ViolinLee/PiHexa18/mechanism/Ver.JX-PDI1181MG/ThighBottom.STL

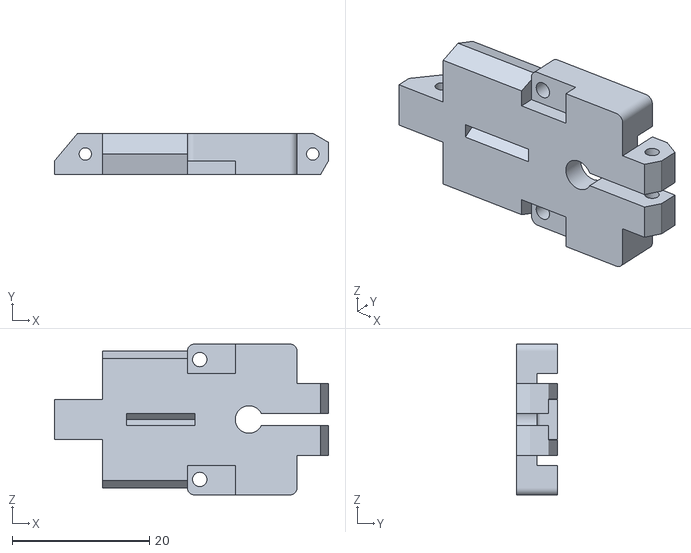
[picture p20: CAD file, 2021-12-25]
mechanism/Ver.JX-PDI1181MG/ThighBottom.STL
40.0 x 6.00 x 22.0
