ViolinLee/PiHexa18/mechanism/Ver.GuoHua-A0090/LegTop.STL

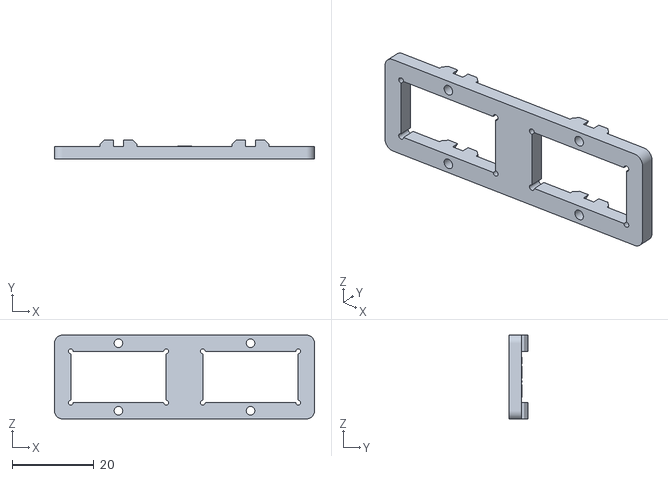
[picture p21: CAD file, 2021-11-15]
mechanism/Ver.GuoHua-A0090/LegTop.STL
63.8 x 4.60 x 20.6
