ViolinLee/PiHexa18/mechanism/Ver.JX-PDI1181MG/JointDown.STL

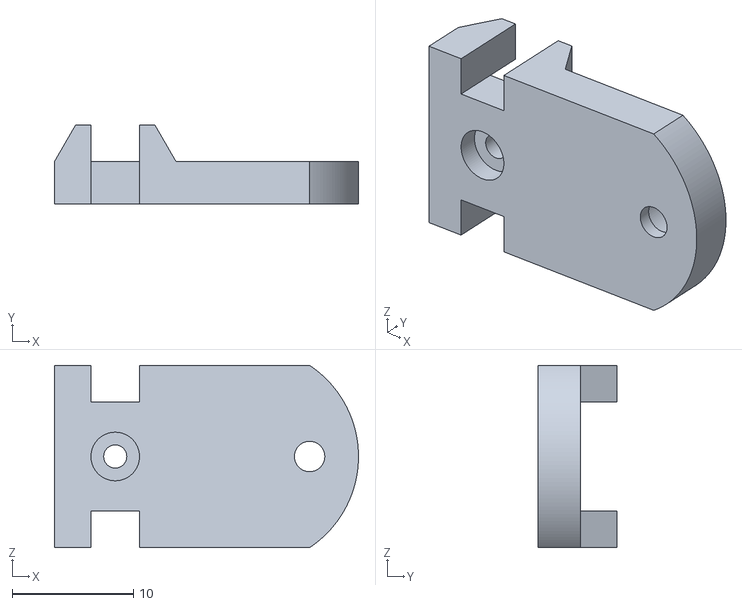
[picture p22: CAD file, 2021-12-25]
mechanism/Ver.JX-PDI1181MG/JointDown.STL
25.0 x 6.50 x 15.0
