ViolinLee/PiHexa18/mechanism/Ver.GuoHua-A0090/LegBottom.STL

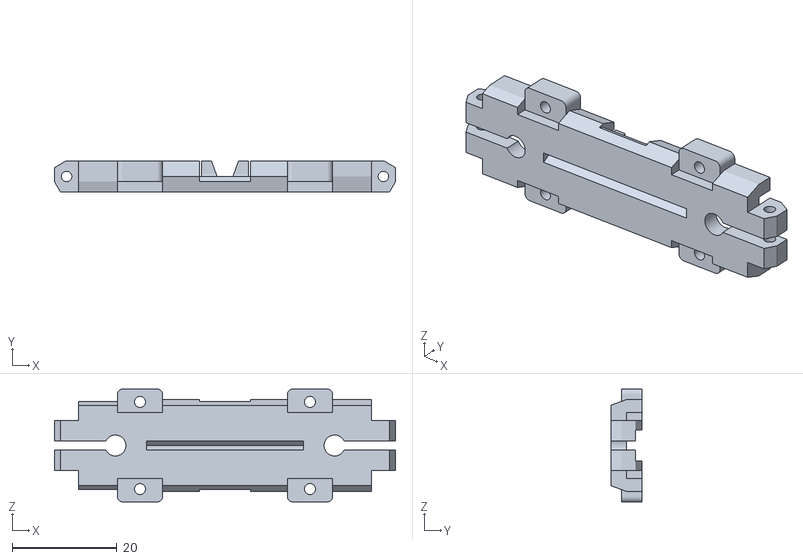
[picture p23: CAD file, 2021-11-15]
mechanism/Ver.GuoHua-A0090/LegBottom.STL
65.0 x 6.00 x 21.5
