ViolinLee/PiHexa18/mechanism/Ver.JX-PDI1181MG/LegBottom.STL

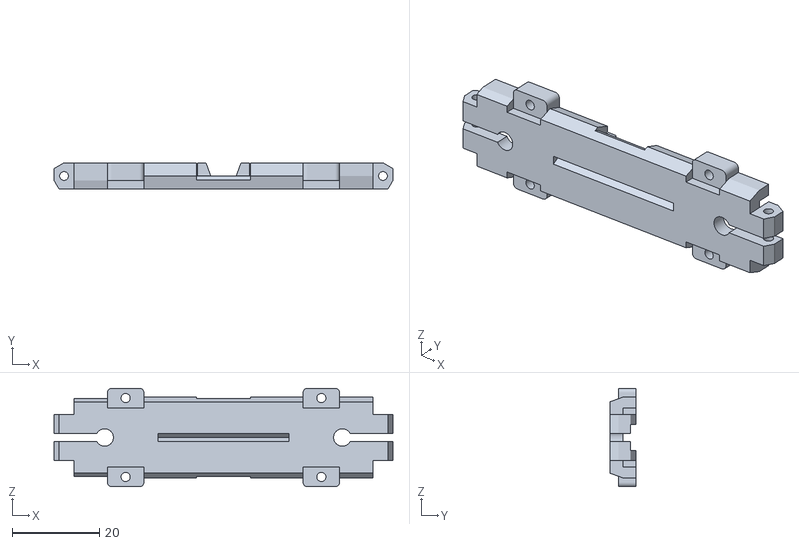
[picture p24: CAD file, 2021-12-25]
mechanism/Ver.JX-PDI1181MG/LegBottom.STL
77.6 x 6.00 x 22.5
