ViolinLee/PiHexa18/mechanism/Ver.GuoHua-A0090/ThighBottom.STL

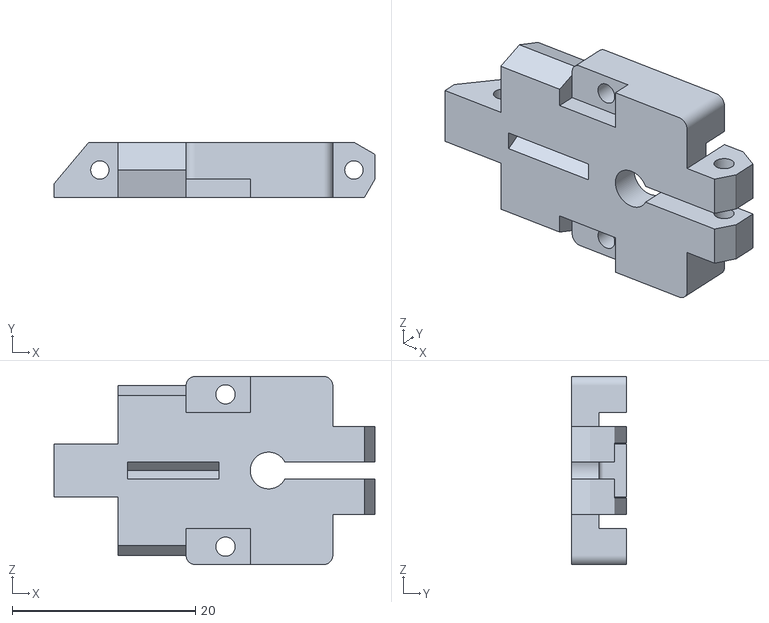
[picture p25: CAD file, 2021-11-15]
mechanism/Ver.GuoHua-A0090/ThighBottom.STL
35.0 x 6.00 x 20.5
