ViolinLee/PiHexa18/mechanism/Ver.JX-PDI1181MG/JointTop.STL

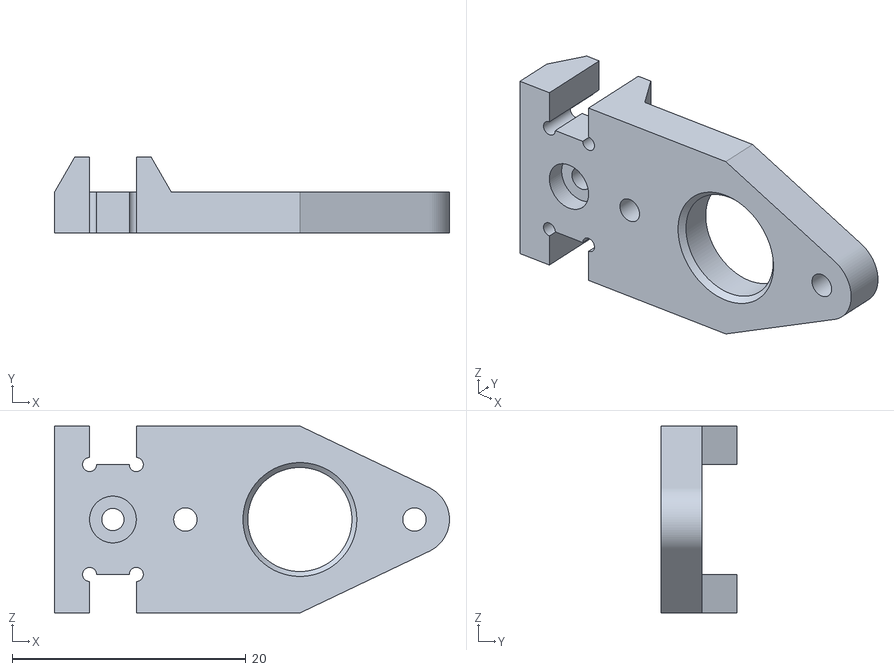
[picture p26: CAD file, 2021-12-25]
mechanism/Ver.JX-PDI1181MG/JointTop.STL
33.8 x 6.50 x 16.0
