ViolinLee/PiHexa18/mechanism/Ver.JX-PDI1181MG/BodySideWall.STL

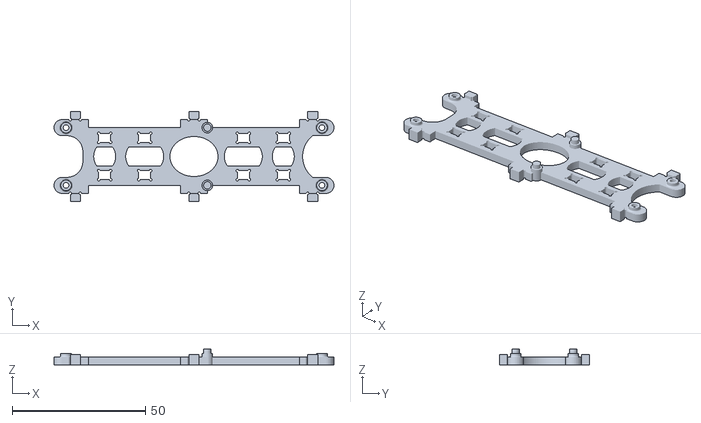
[picture p27: CAD file, 2021-12-23]
mechanism/Ver.JX-PDI1181MG/BodySideWall.STL
105.0 x 33.7 x 6.00
