ViolinLee/PiHexa18/mechanism/Ver.JX-PDI1181MG/BodyCenter.STL

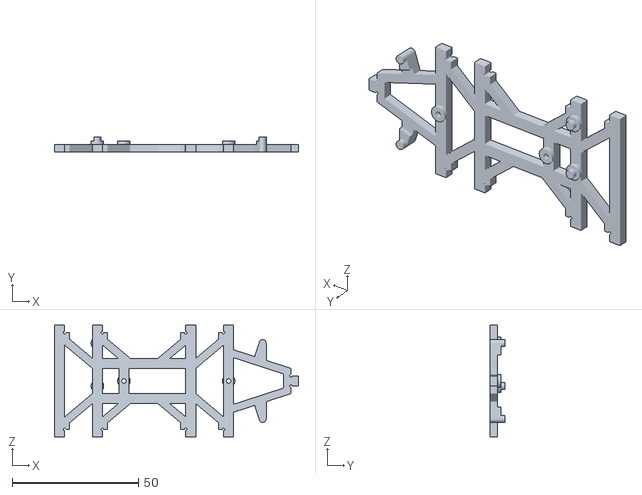
[picture p28: CAD file, 2021-12-23]
mechanism/Ver.JX-PDI1181MG/BodyCenter.STL
96.7 x 6.00 x 44.3
