ViolinLee/PiHexa18/mechanism/Ver.JX-PDI1181MG/FootTip.STL

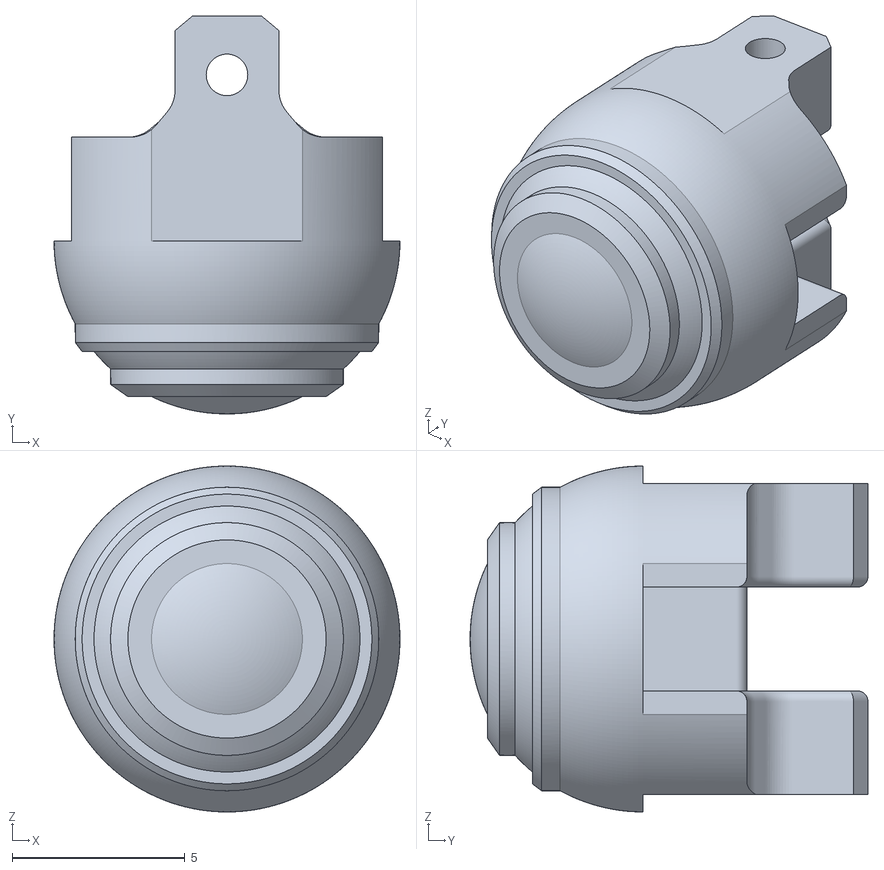
[picture p29: CAD file, 2021-12-23]
mechanism/Ver.JX-PDI1181MG/FootTip.STL
10.0 x 11.5 x 10.00
