ViolinLee/PiHexa18/mechanism/Ver.JX-PDI1181MG/BodyBackWall.STL

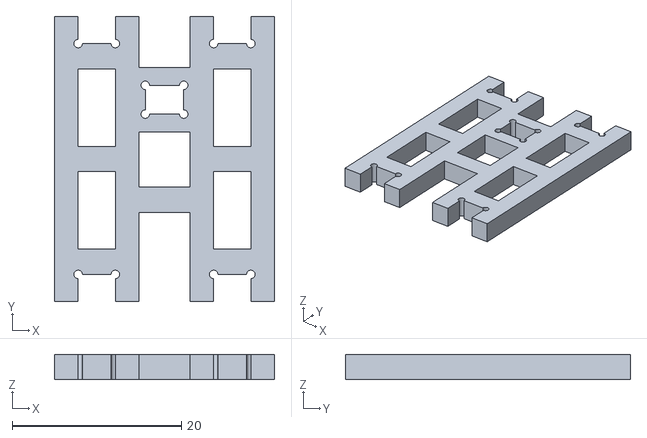
[picture p30: CAD file, 2021-12-22]
mechanism/Ver.JX-PDI1181MG/BodyBackWall.STL
26.0 x 33.7 x 3.00
