ViolinLee/PiHexa18/mechanism/Ver.JX-PDI1181MG/BodyButtom.STL

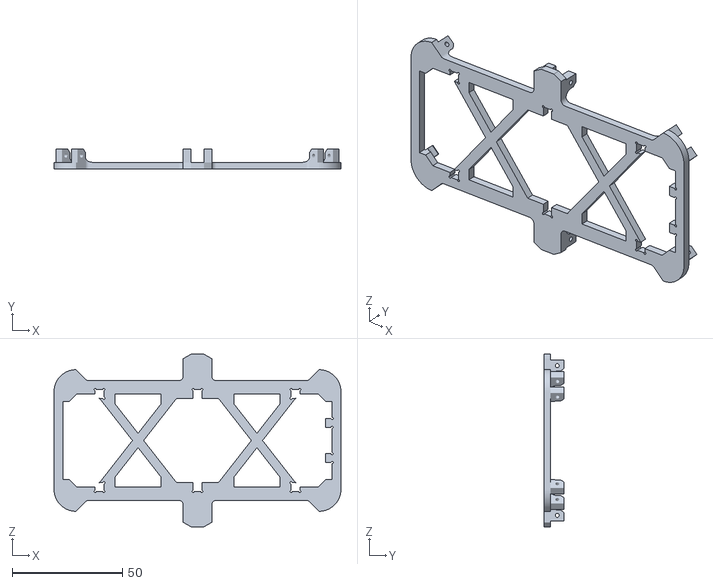
[picture p31: CAD file, 2021-12-22]
mechanism/Ver.JX-PDI1181MG/BodyButtom.STL
130.3 x 9.00 x 78.3
