ViolinLee/PiHexa18/pihexa/leg.py

# -*- coding: utf-8 -*-

from config import *
from math_utils import *
from math import sin, cos, pi, atan2, sqrt, acos


hpi = pi/2


class BaseLeg(object):
    def __init__(self, leg_index):
        self._leg_index = leg_index
        """ 
        local_conv: 世界坐标系上的表达转换到本地坐标系上的表达
        world_conv: 本地坐标系上的表达转换到世界坐标系上的表达
        """
        if self._leg_index == 0:  # 45 or -315 degree:
            self._mount_position = point3d(leg_mount_other_x, leg_mount_other_y, 0)
            self._local_conv = rotate315  # local_P = R(local上world下，world在local上的描述) * world_P
            self._world_conv = rotate45  # world_P = R(world上local下，local在world上的描述) * local_P
            self._tip_pos_local = point3d(p1_x, p1_y, p1_z)
            self._tip_pos = self.translate2world(self._tip_pos_local)
        elif self._leg_index == 1:  # 0 degree:
            self._mount_position = point3d(leg_mount_left_right_x, 0, 0)
            self._local_conv = rotate0
            self._world_conv = rotate0
            self._tip_pos_local = point3d(p2_x, p2_y, p2_z)
            self._tip_pos = self.translate2world(self._tip_pos_local)
        elif self._leg_index == 2:  # -45 or 315 degree:
            self._mount_position = point3d(leg_mount_other_x, -leg_mount_other_y, 0)
            self._local_conv = rotate45
            self._world_conv = rotate315
            self._tip_pos_local = point3d(p3_x, p3_y, p3_z)
            self._tip_pos = self.translate2world(self._tip_pos_local)
        elif self._leg_index == 3:  # -135 or 225 degree:
            self._mount_position = point3d(-leg_mount_other_x, -leg_mount_other_y, 0)
            self._local_conv = rotate135
            self._world_conv = rotate225
            self._tip_pos_local = point3d(p4_x, p4_y, p4_z)
            self._tip_pos = self.translate2world(self._tip_pos_local)
        elif self._leg_index == 4:  # -180 or 180 degree:
            self._mount_position = point3d(-leg_mount_left_right_x, 0, 0)
            self._local_conv = rotate180
            self._world_conv = rotate180
            self._tip_pos_local = point3d(p5_x, p5_y, p5_z)
            self._tip_pos = self.translate2world(self._tip_pos_local)
        elif self._leg_index == 5:  # -225 or 135 degree:
            self._mount_position = point3d(-leg_mount_other_x, leg_mount_other_y, 0)
            self._local_conv = rotate225
            self._world_conv = rotate135
            self._tip_pos_local = point3d(p6_x, p6_y, p6_z)
            self._tip_pos = self.translate2world(self._tip_pos_local)
        else:
            raise ValueError

    """coordinate system translation"""
    def translate2local(self, world_point: point3d):
        return self._local_conv(world_point - self._mount_position)

    def translate2world(self, local_point: point3d):
        return self._world_conv(local_point) + self._mount_position

    @staticmethod
    def inverse_kinematics(target_point: point3d):
        """坐标原点在根部舵机安装处"""
        angles = [0.0] * 3

        x = target_point.x - leg_root2joint1
        y = target_point.y
        angles[0] = atan2(y, x) * 180 / pi

        x = sqrt(x**2 + y**2) - leg_joint1_2joint2
        y = target_point.z
        ar = atan2(y, x)
        lr2 = x**2 + y**2
        lr = sqrt(lr2)
        a1 = acos((lr2 + leg_joint2_2joint3**2 - leg_joint3_2tip**2) / (2 * leg_joint2_2joint3 * lr))
        a2 = acos((lr2 - leg_joint2_2joint3**2 + leg_joint3_2tip**2) / (2 * leg_joint3_2tip * lr))
        angles[1] = (ar + a1) * 180 / pi
        angles[2] = 90 - ((a1 + a2) * 180 / pi)

        return angles

    def get_tip_position_local(self):
        return self._tip_pos_local


class RealLeg(BaseLeg):
    """
    定义六足机器人单腿类，包括基坐标转换和正逆运动学相关类函数。
    """
    def __init__(self, leg_index, leg_servo):
        super().__init__(leg_index)
        self._leg_servo = leg_servo

    """forward and inverse kinematics calculations are below local coordinate"""
    @staticmethod
    def forward_kinematics(angles):
        radians = [angle * pi / 180 for angle in angles]
        x = leg_joint1_2joint2 + cos(radians[1]) * leg_joint2_2joint3 + cos(radians[1] + radians[2] - hpi) * leg_joint3_2tip

        out_point = point3d()
        out_point.x = leg_root2joint1 + cos(radians[0]) * x
        out_point.y = sin(radians[0]) * x
        out_point.z = sin(radians[1]) * leg_joint2_2joint3 + sin(radians[1] + radians[2] - hpi) * leg_joint3_2tip

        return out_point

    def set_joint_angle(self, angles):
        out_point = self.forward_kinematics(angles)
        self.move_tip_local(out_point)

    def move_tip(self, target_point_world: point3d):
        """word coordiante system (default)"""
        if target_point_world == self._tip_pos:
            return
        dest_local = self.translate2local(target_point_world)
        # logging info
        self.__move(dest_local)
        self._tip_pos = target_point_world
        self._tip_pos_local = dest_local

    def get_tip_position(self):
        return self._tip_pos

    def move_tip_local(self, target_point_local: point3d):
        """local coordinate system version"""
        if target_point_local == self._tip_pos_local:
            return
        dest_world = self.translate2world(target_point_local)
        self.__move(target_point_local)
        self._tip_pos = dest_world
        self._tip_pos_local = target_point_local

    def __move(self, target_point_local: point3d):
        angles = self.inverse_kinematics(target_point_local)
        # Logging info
        for i in range(3):
            self._leg_servo.set_angle(self._leg_index, i, angles[i])


class VirtualLeg(BaseLeg):
    def __init__(self, leg_index):
        super(VirtualLeg, self).__init__(leg_index)
        self.joint_angles = [0, 30, -15]
        self.leg_vectors_local = self.forward_kinematics(self.joint_angles)
        self.leg_vectors = [self.translate2world(point) for point in self.leg_vectors_local]

    @staticmethod
    def forward_kinematics(angles):
        """leg_vectors: point3d list with length of 5"""
        radians = [angle * pi / 180 for angle in angles]
        joint1_pos = point3d(leg_root2joint1, 0, 0)
        joint2_pos = joint1_pos + point3d(leg_joint1_2joint2 * cos(radians[0]), leg_joint1_2joint2 * sin(radians[0]), 0)
        joint3_pos = joint2_pos + point3d(leg_joint2_2joint3 * cos(radians[1]) * cos(radians[0]),
                                          leg_joint2_2joint3 * cos(radians[1]) * sin(radians[0]),
                                          leg_joint2_2joint3 * sin(radians[1]))
        joint4_pos = joint3_pos + point3d(cos(radians[1] + radians[2] - hpi) * leg_joint3_2tip * cos(radians[0]),
                                          cos(radians[1] + radians[2] - hpi) * leg_joint3_2tip * sin(radians[0]),
                                          sin(radians[1] + radians[2] - hpi) * leg_joint3_2tip)

        leg_vectors_local = [point3d(0, 0, 0), joint1_pos, joint2_pos, joint3_pos, joint4_pos]

        return leg_vectors_local
    
    def move_tip(self, target_point_world: point3d):
        if target_point_world == self._tip_pos:
            return
        dest_local = self.translate2local(target_point_world)
        # logging info
        self.__move(dest_local)
        self._tip_pos = target_point_world
        self._tip_pos_local = dest_local

    def __move(self, target_point_local: point3d):
        angles = self.inverse_kinematics(target_point_local)
        self.joint_angles = angles
        # To simulate movement on matplotlib figure
        self.leg_vectors_local = self.forward_kinematics(angles)
        self.leg_vectors = [self.translate2world(point) for point in self.leg_vectors_local]
